crice009/toolauth-hardware/docs/img/buzz.jpg

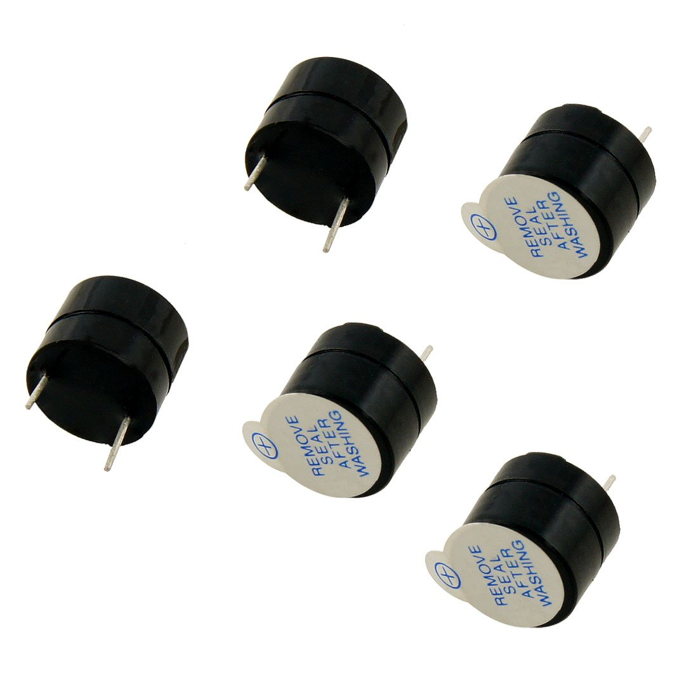
docs/img/buzz.jpg
