crice009/toolauth-hardware/docs/img/current-clamp.jpg

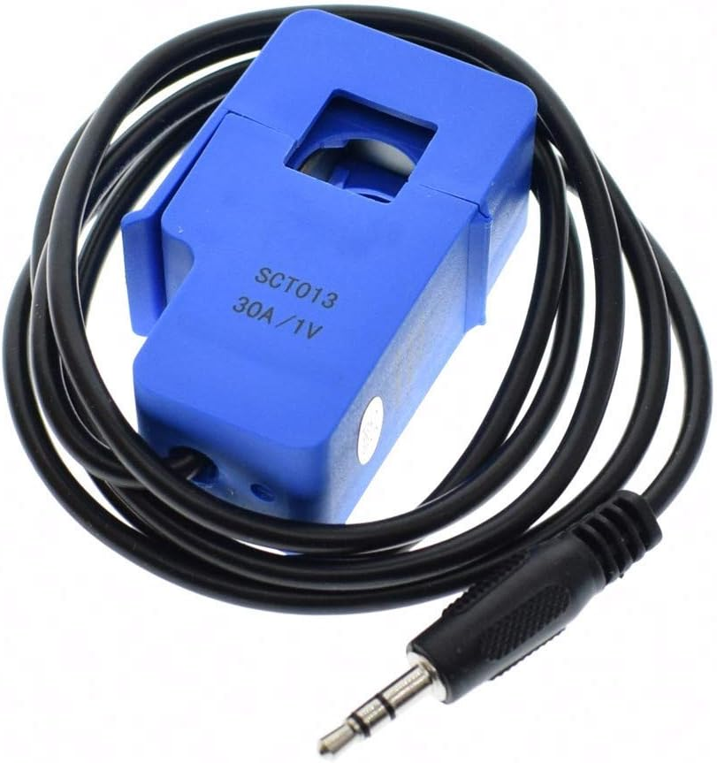
docs/img/current-clamp.jpg
