crice009/toolauth-hardware/docs/img/eink.jpg

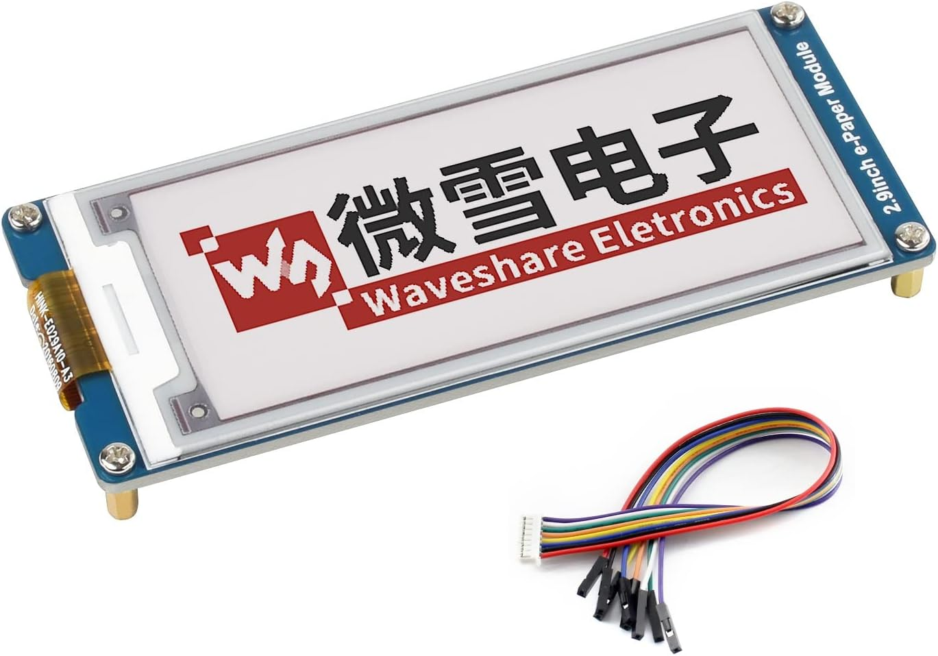
docs/img/eink.jpg
