crice009/toolauth-hardware/docs/img/estop-config.png

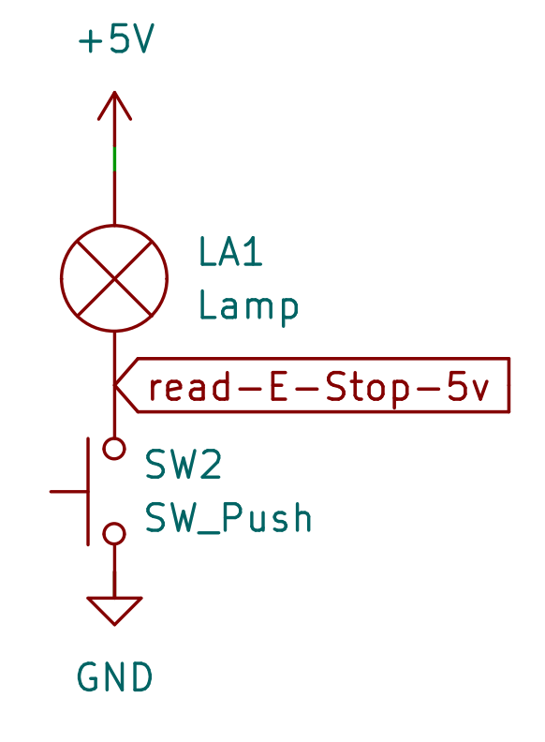
docs/img/estop-config.png
