crice009/toolauth-hardware/docs/img/estop-jst.png

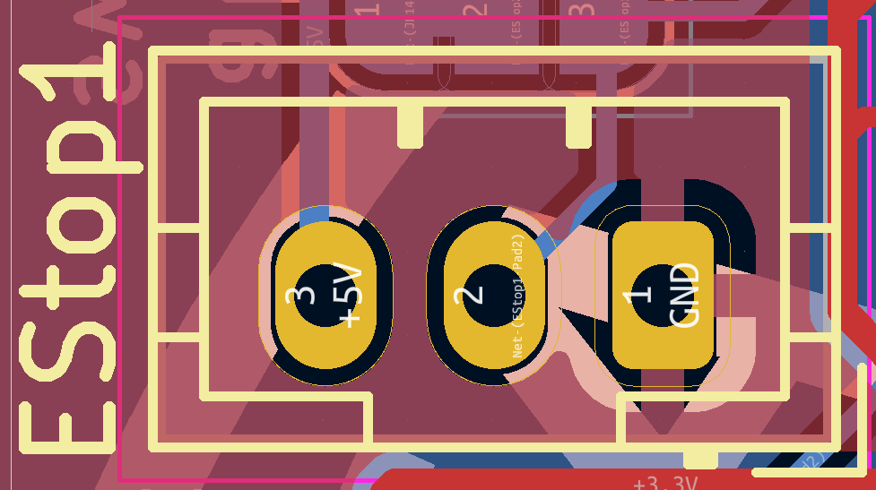
docs/img/estop-jst.png
