crice009/toolauth-hardware/docs/img/led.jpg

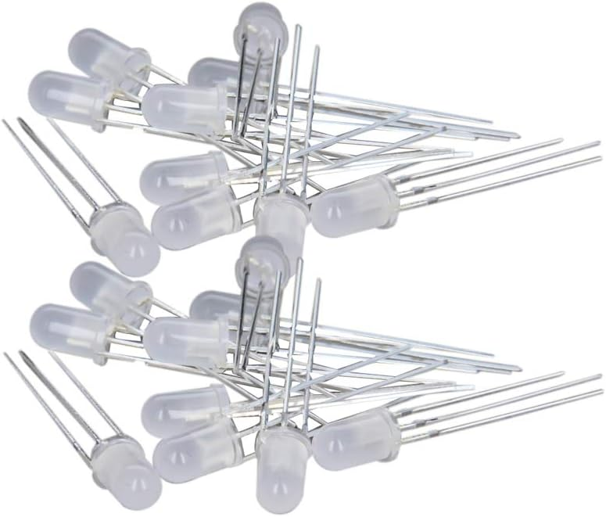
docs/img/led.jpg
