crice009/toolauth-hardware/docs/img/pn532-board.jpg

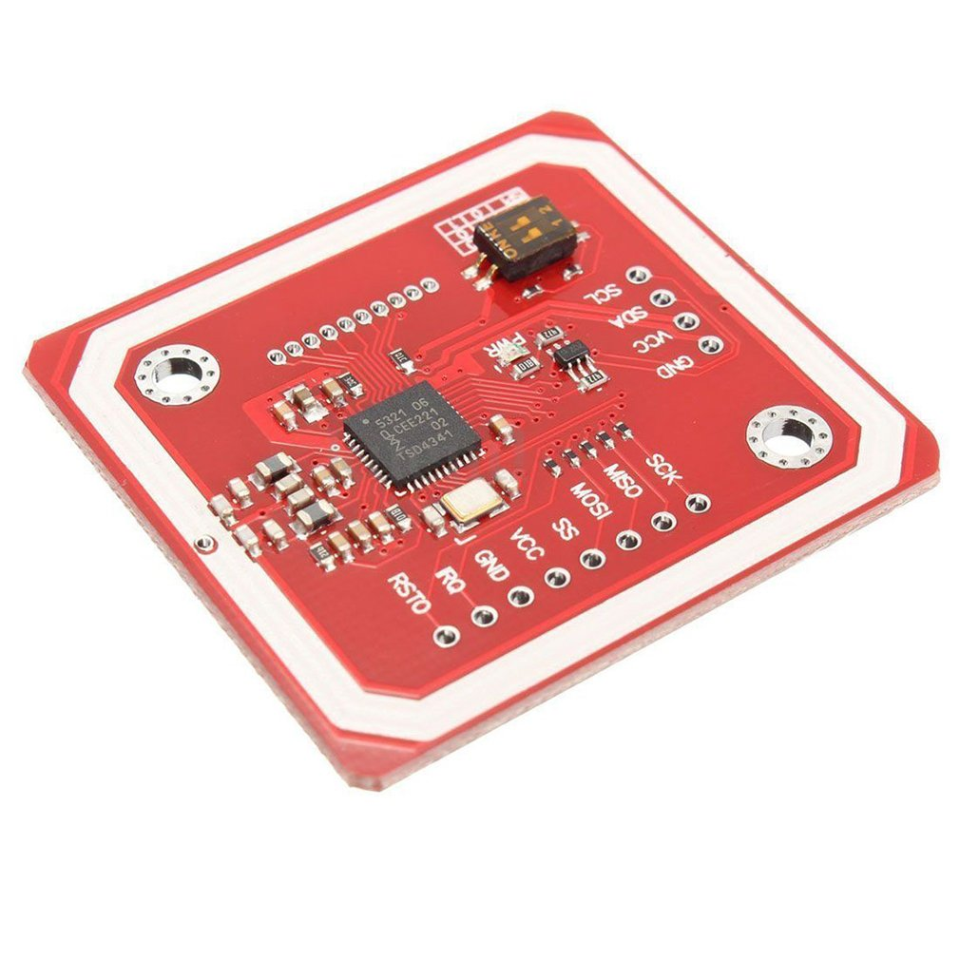
docs/img/pn532-board.jpg
