crice009/toolauth-hardware/docs/img/rd-3d.png

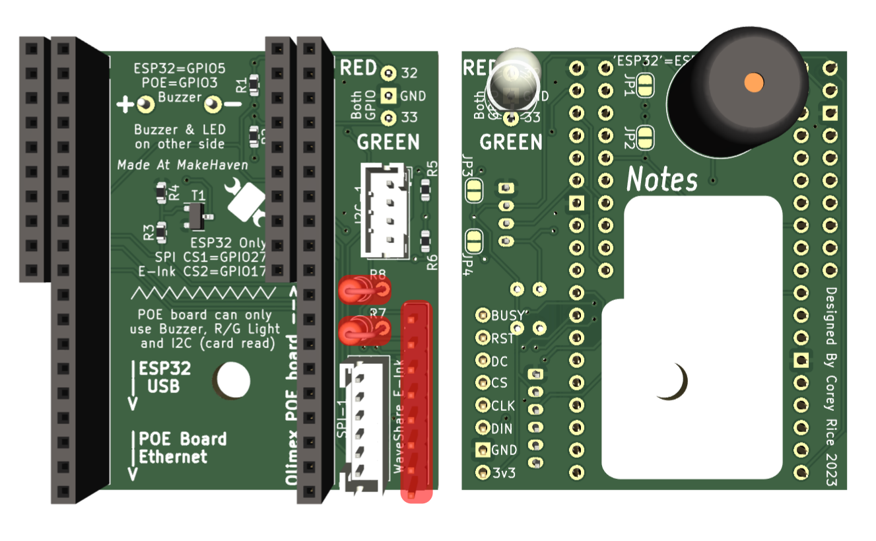
docs/img/rd-3d.png
