crice009/toolauth-hardware/docs/img/rd-back-unpop.png

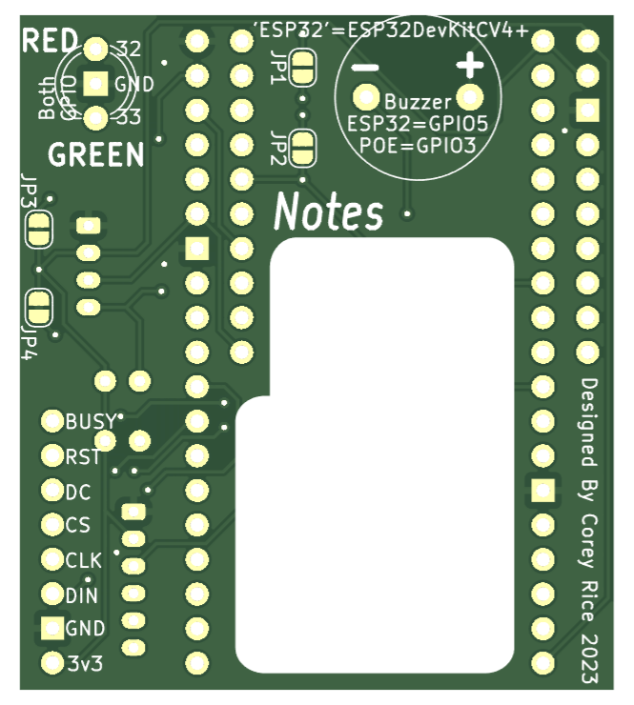
docs/img/rd-back-unpop.png
