crice009/toolauth-hardware/docs/img/rd-back.png

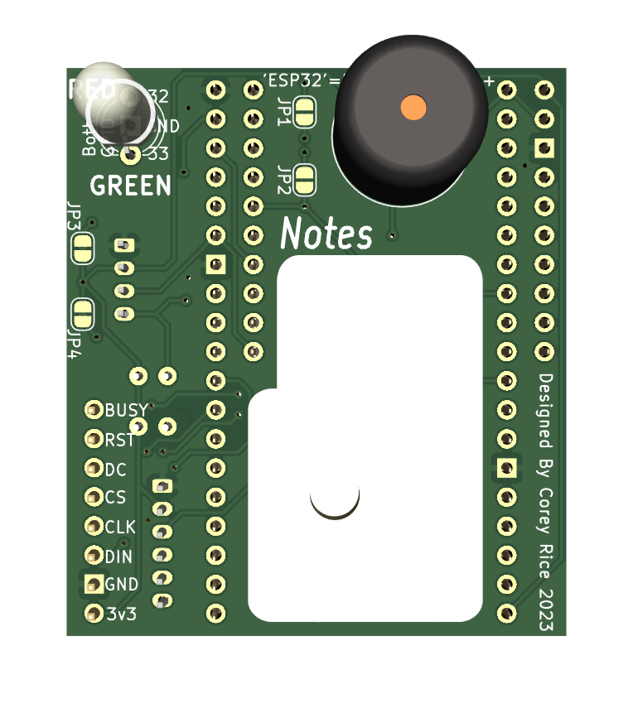
docs/img/rd-back.png
