crice009/toolauth-hardware/docs/img/rd-buzzer-rear.png

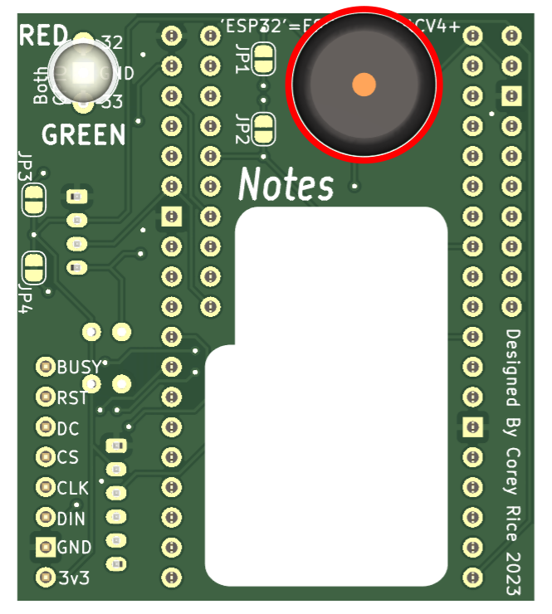
docs/img/rd-buzzer-rear.png
