crice009/toolauth-hardware/docs/img/rd-buzzer.png

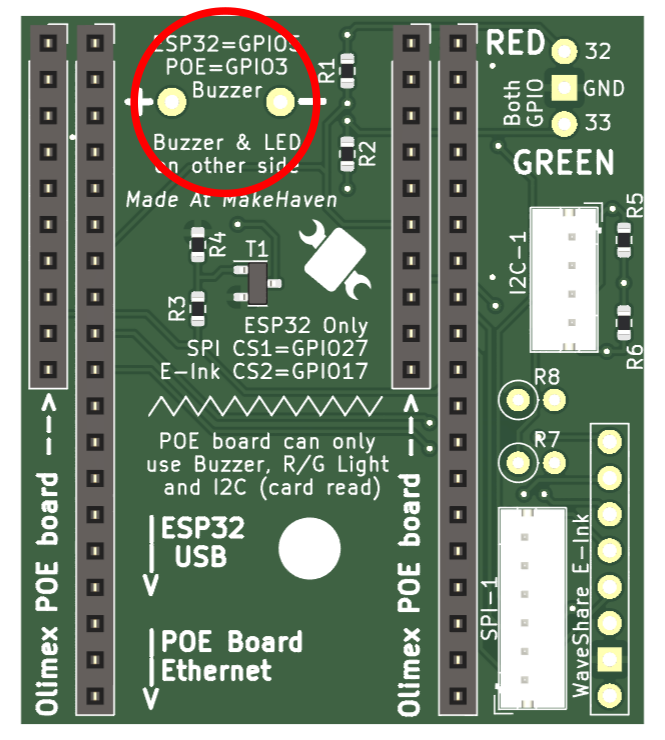
docs/img/rd-buzzer.png
