crice009/toolauth-hardware/docs/img/rd-front.png

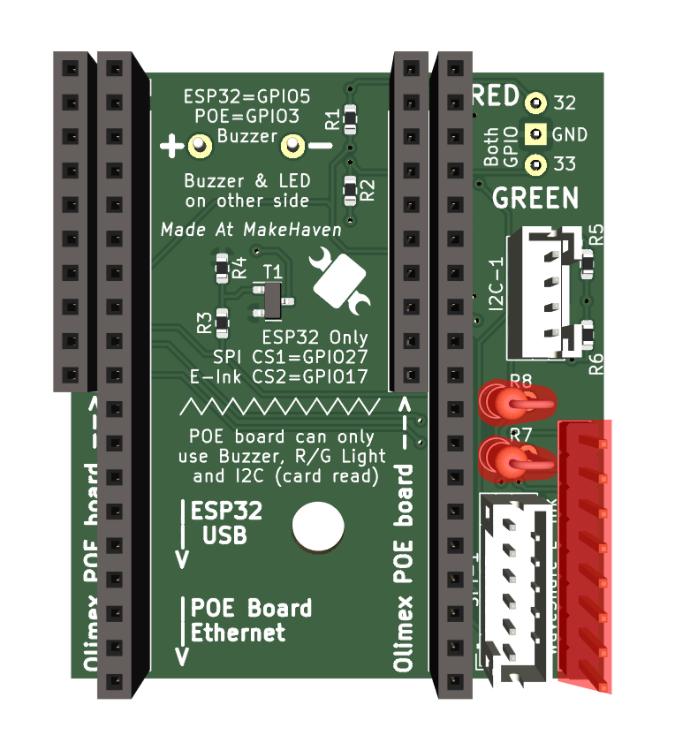
docs/img/rd-front.png
