crice009/toolauth-hardware/docs/img/reader-daughter-rear.png

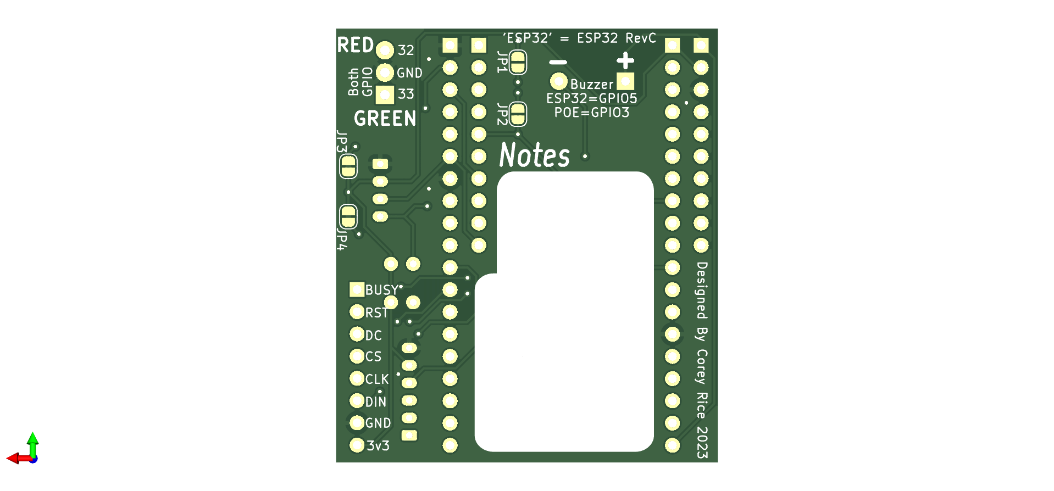
docs/img/reader-daughter-rear.png
