crice009/toolauth-hardware/docs/img/v1.3-5vpower.png

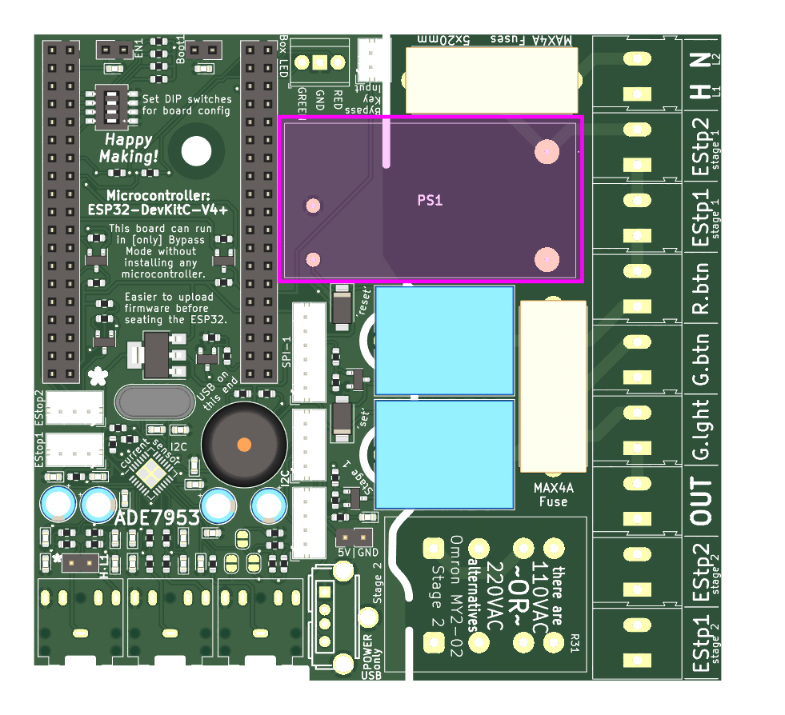
docs/img/v1.3-5vpower.png
