crice009/toolauth-hardware/reader-daughter/geometry/olimex-poe-iso.png

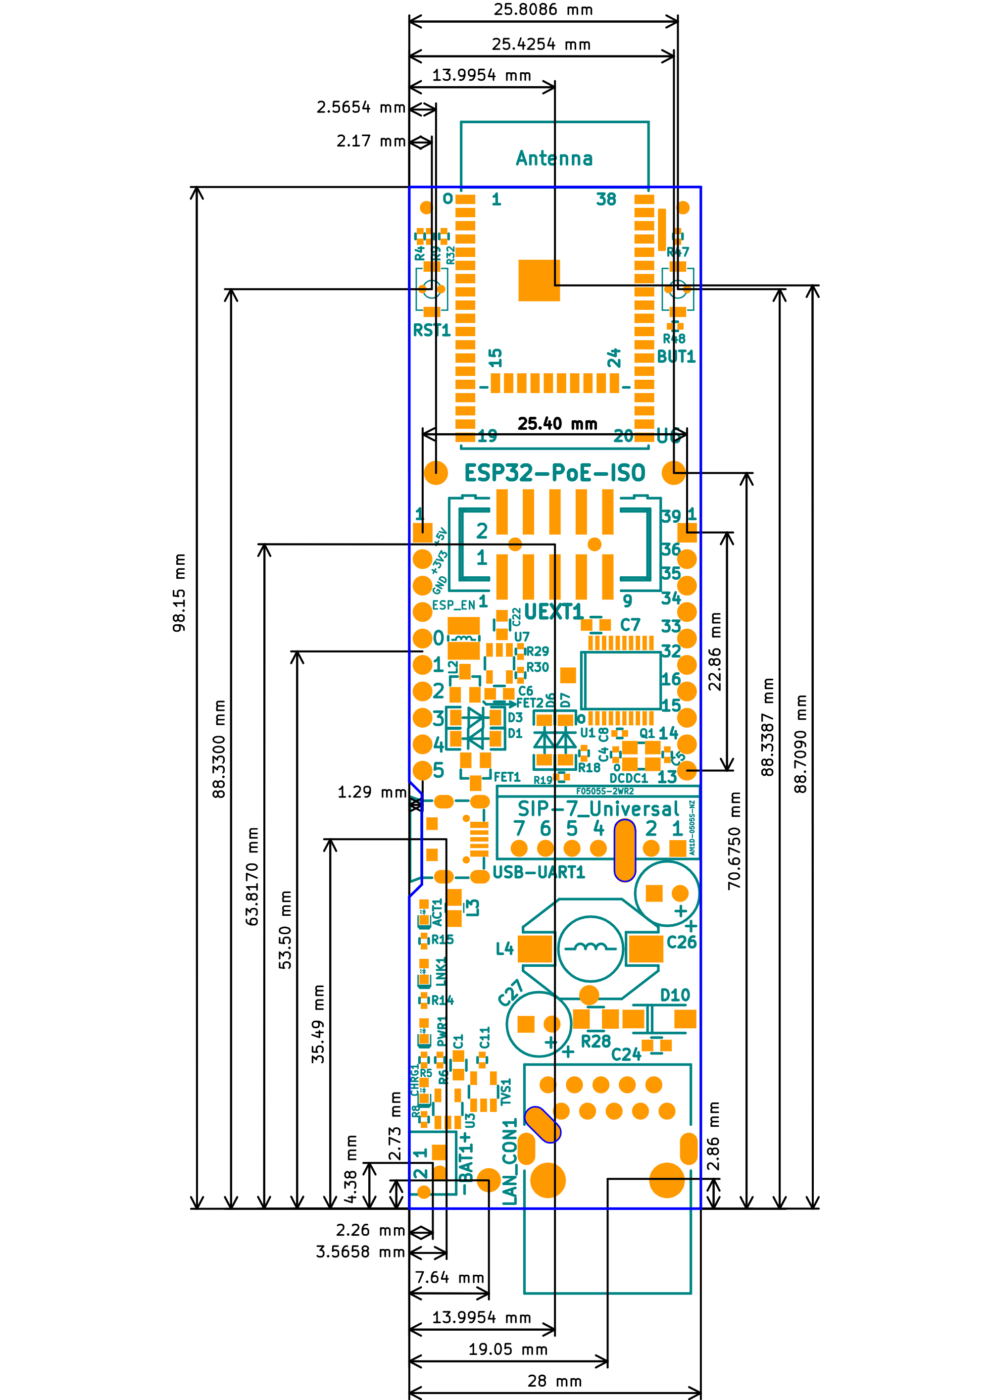
reader-daughter/geometry/olimex-poe-iso.png
