crice009/toolauth-hardware/V1.3/odd-parts/CFM06S050-E-Cincon/5vdc-size.PNG

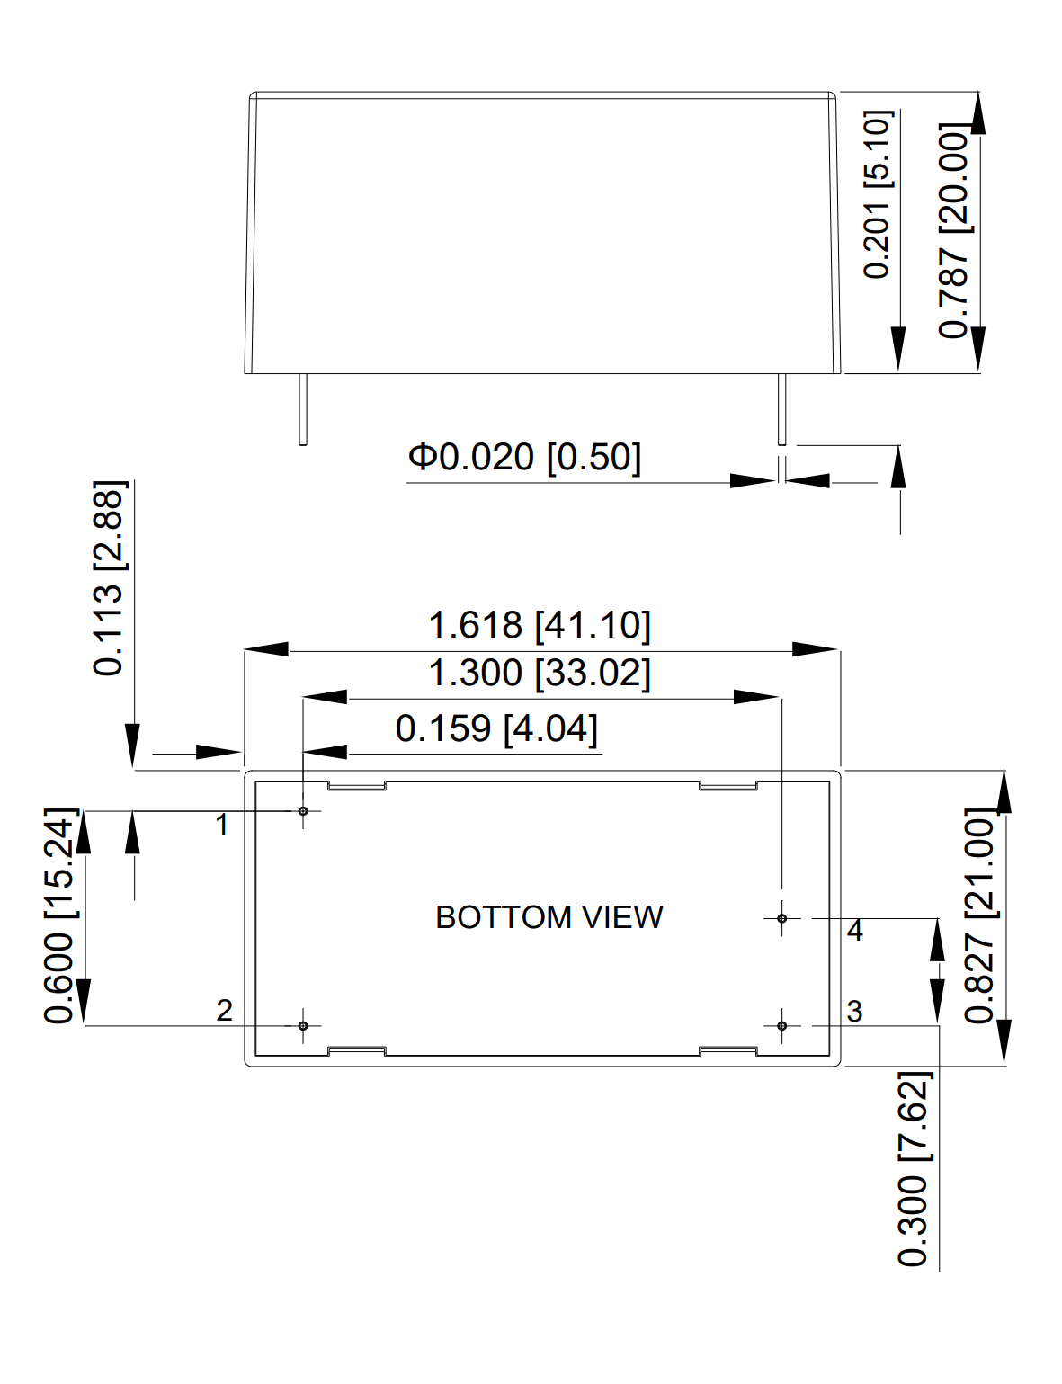
V1.3/odd-parts/CFM06S050-E-Cincon/5vdc-size.PNG
